bolwire/OGX360I-4CH/Images/20210410_085436.jpg

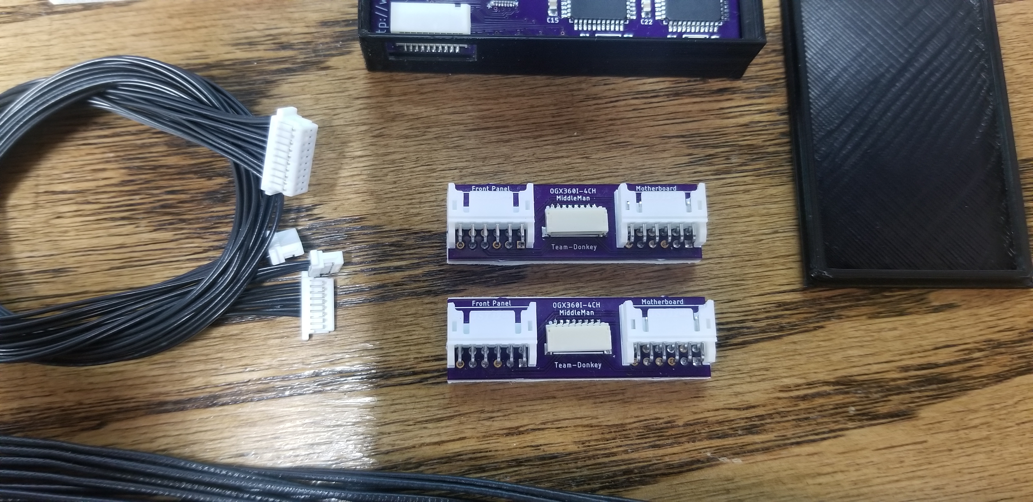
Images/20210410_085436.jpg
