bolwire/OGX360I-4CH/Images/20210410_085500.jpg

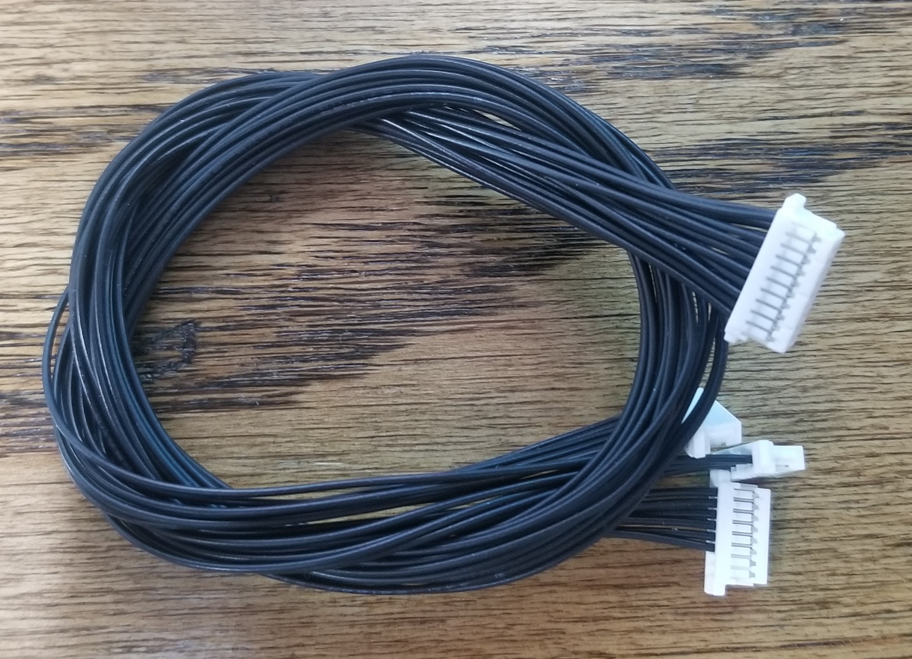
Images/20210410_085500.jpg
