bolwire/OGX360I-4CH/Images/20210410_085641.jpg

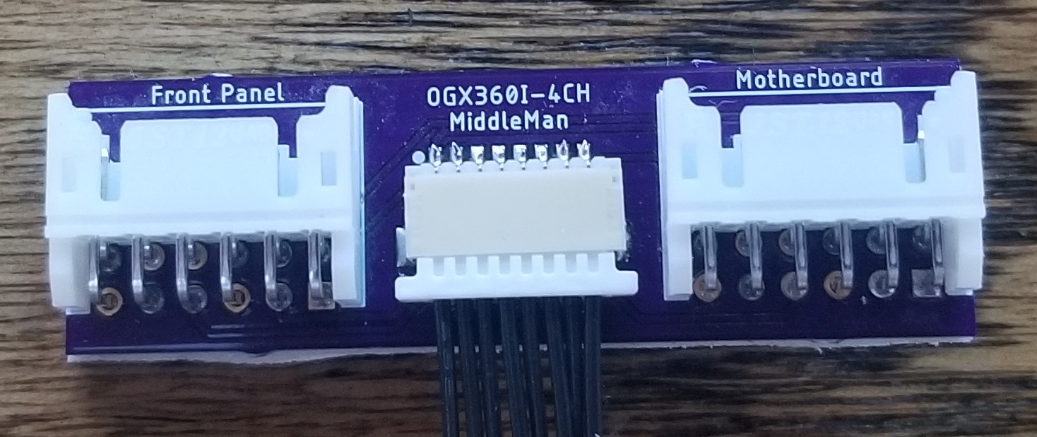
Images/20210410_085641.jpg
