bolwire/OGX360I-4CH/Images/20210410_085656.jpg

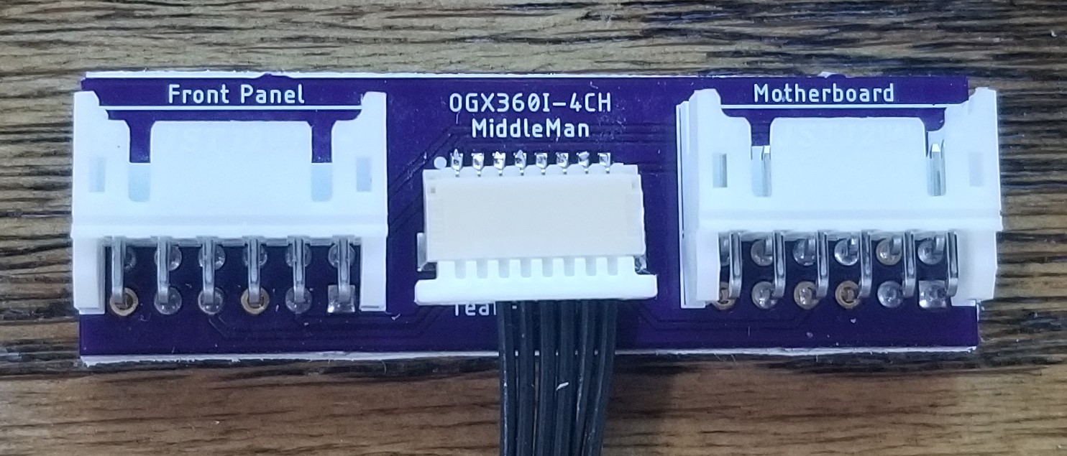
Images/20210410_085656.jpg
