bolwire/OGX360I-4CH/Images/20210410_085711.jpg

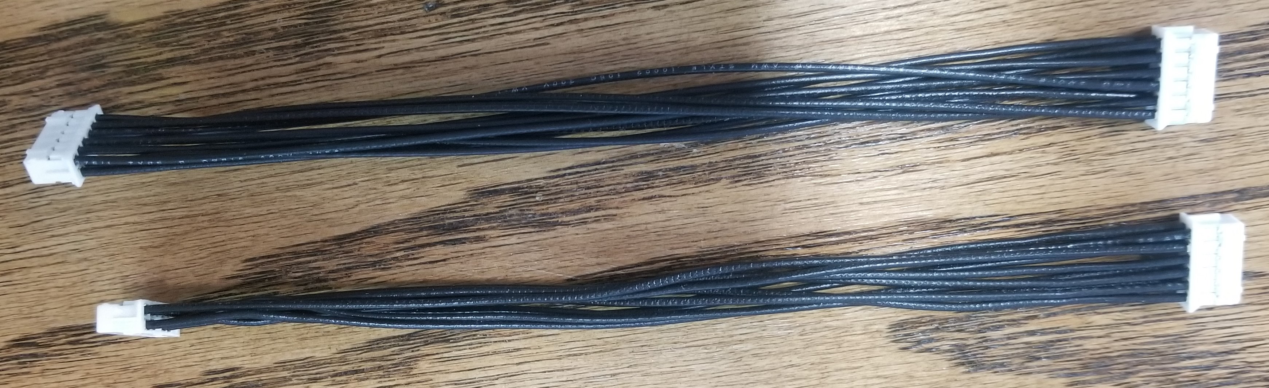
Images/20210410_085711.jpg
